mahir-mahota/322-Project-2/SOLIDWORKS_P1/Bearing_H_61952_ma_2.SLDASM

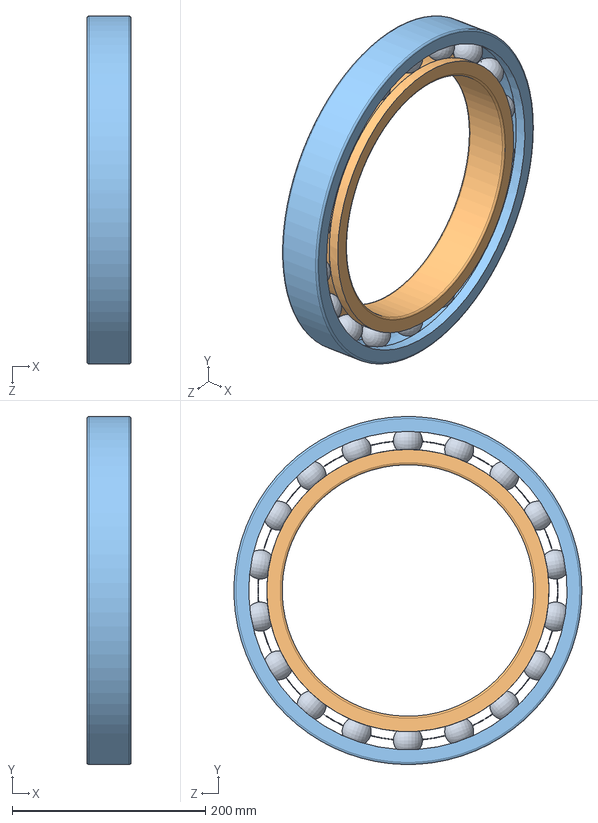
[picture p13: CAD file, 2025-11-18]
SOLIDWORKS_P1/Bearing_H_61952_ma_2.SLDASM
46.0 x 360.0 x 359.8 mm
skf_bearing_61952_ma_2_01
skf_bearing_61952_ma_2_02
skf_bearing_61952_ma_2_03
