mahir-mahota/322-Project-2/SOLIDWORKS_P1/skf_bearing_61952_ma_2_02.SLDPRT

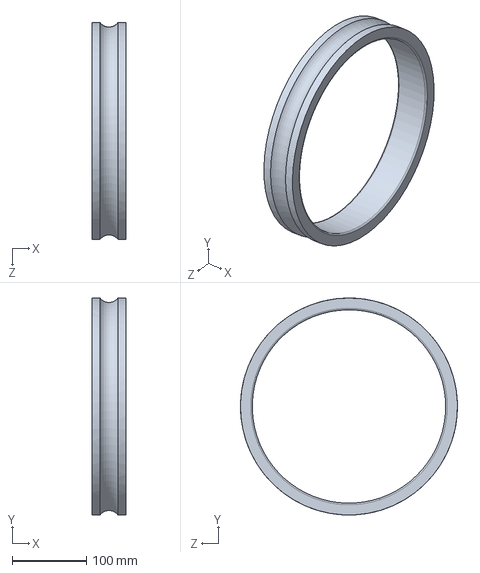
[picture p21: CAD file, 2025-11-18]
SOLIDWORKS_P1/skf_bearing_61952_ma_2_02.SLDPRT
46.0 x 291.9 x 291.8 mm
