mahir-mahota/322-Project-2/SOLIDWORKS_P1/Brg_K_outer_cover2.SLDPRT

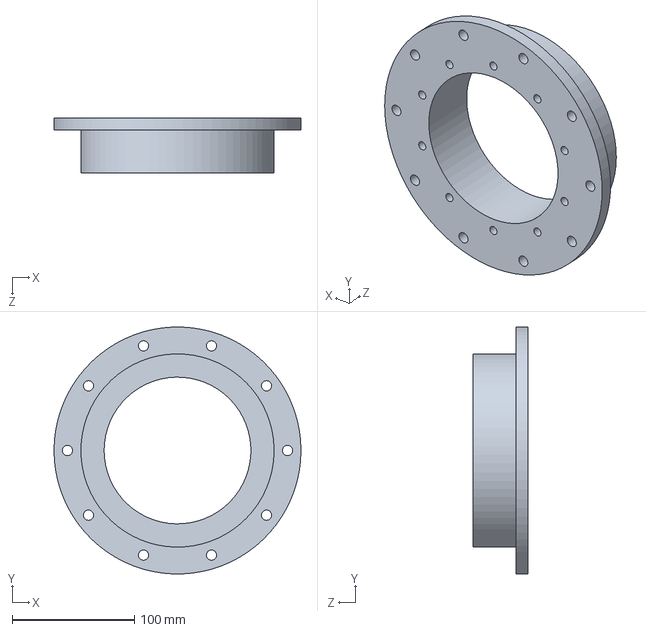
[picture p22: CAD file, 2025-11-18]
SOLIDWORKS_P1/Brg_K_outer_cover2.SLDPRT
202.0 x 201.8 x 45.0 mm
