mahir-mahota/322-Project-2/SOLIDWORKS_P2/Input_shaft_assay_4_Proj2/Input_shaft.SLDPRT

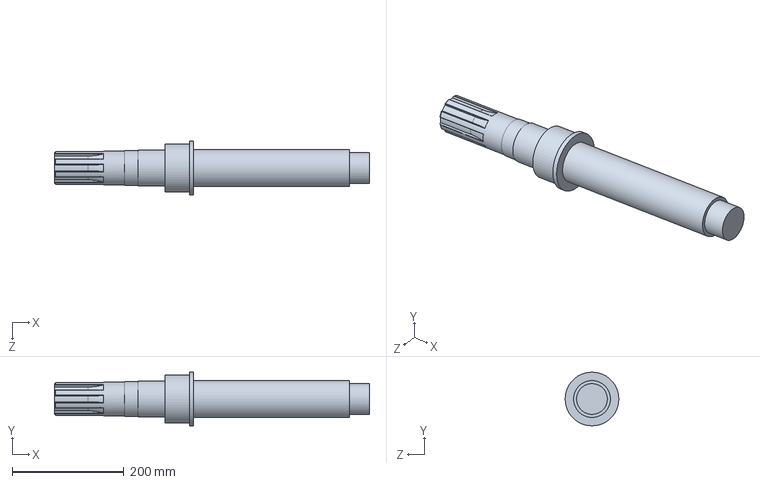
[picture p23: CAD file, 2025-11-28]
SOLIDWORKS_P2/Input_shaft_assay_4_Proj2/Input_shaft.SLDPRT
563.2 x 96.0 x 96.0 mm
