mahir-mahota/322-Project-2/SOLIDWORKS_P1/skf_bearing_na_4840_2_03.SLDPRT

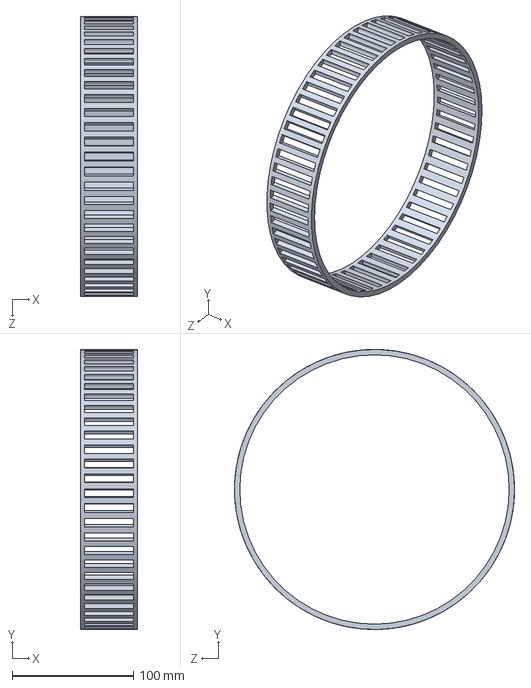
[picture p24: CAD file, 2025-11-18]
SOLIDWORKS_P1/skf_bearing_na_4840_2_03.SLDPRT
47.0 x 230.6 x 230.6 mm
