mahir-mahota/322-Project-2/SOLIDWORKS_P2/Input_shaft_assay_4_Proj2/Housing_input.SLDPRT

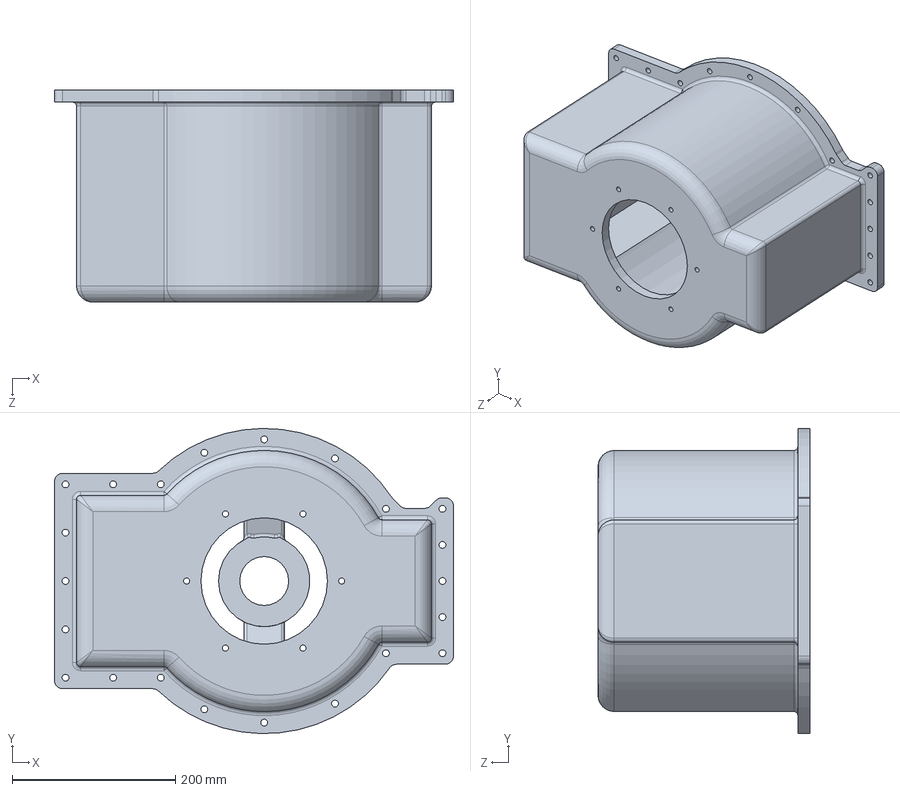
[picture p25: CAD file, 2025-11-28]
SOLIDWORKS_P2/Input_shaft_assay_4_Proj2/Housing_input.SLDPRT
489.0 x 373.9 x 260.0 mm
