mahir-mahota/322-Project-2/SOLIDWORKS_P2/Input_shaft_assay_4_Proj2/Housing_input_cover.SLDPRT

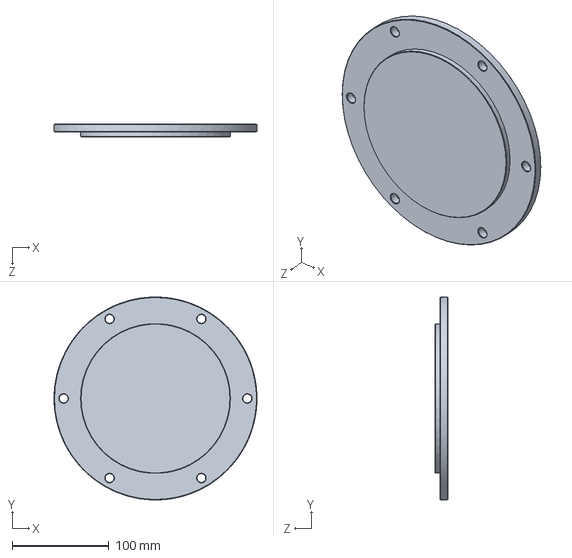
[picture p26: CAD file, 2025-11-20]
SOLIDWORKS_P2/Input_shaft_assay_4_Proj2/Housing_input_cover.SLDPRT
210.0 x 209.9 x 13.0 mm
