mahir-mahota/322-Project-2/SOLIDWORKS_P1/Azi_pinion.SLDPRT

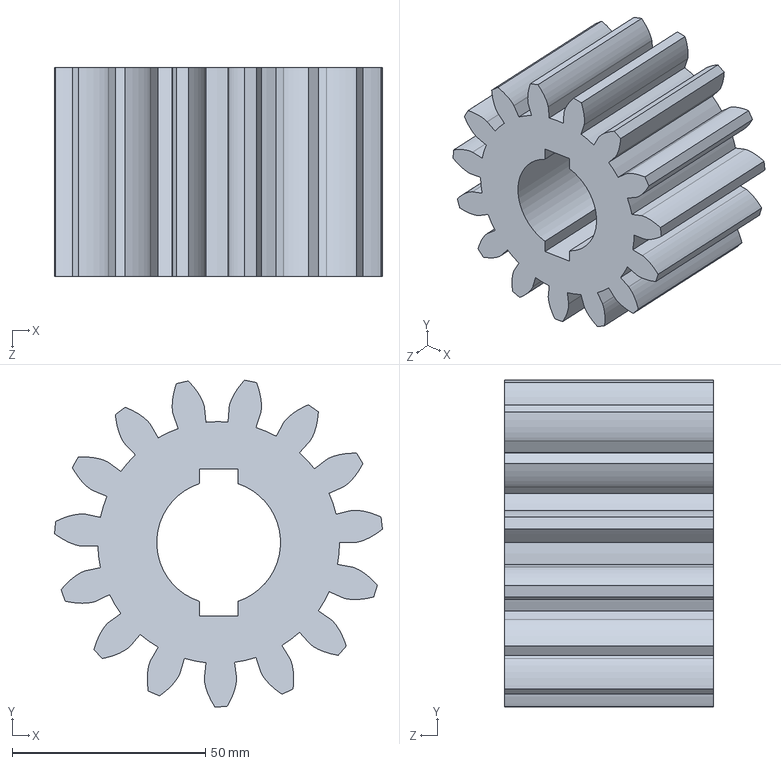
[picture p27: CAD file, 2025-11-18]
SOLIDWORKS_P1/Azi_pinion.SLDPRT
84.8 x 84.5 x 54.0 mm
