mahir-mahota/322-Project-2/SOLIDWORKS_P1/Rudder_tube.SLDPRT

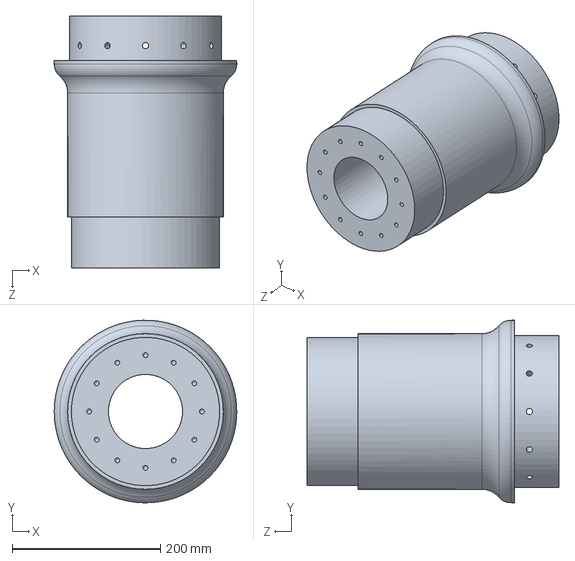
[picture p28: CAD file, 2025-11-18]
SOLIDWORKS_P1/Rudder_tube.SLDPRT
246.3 x 246.3 x 340.0 mm
