mahir-mahota/322-Project-2/SOLIDWORKS_P1/Azi_seal_housing2.SLDPRT

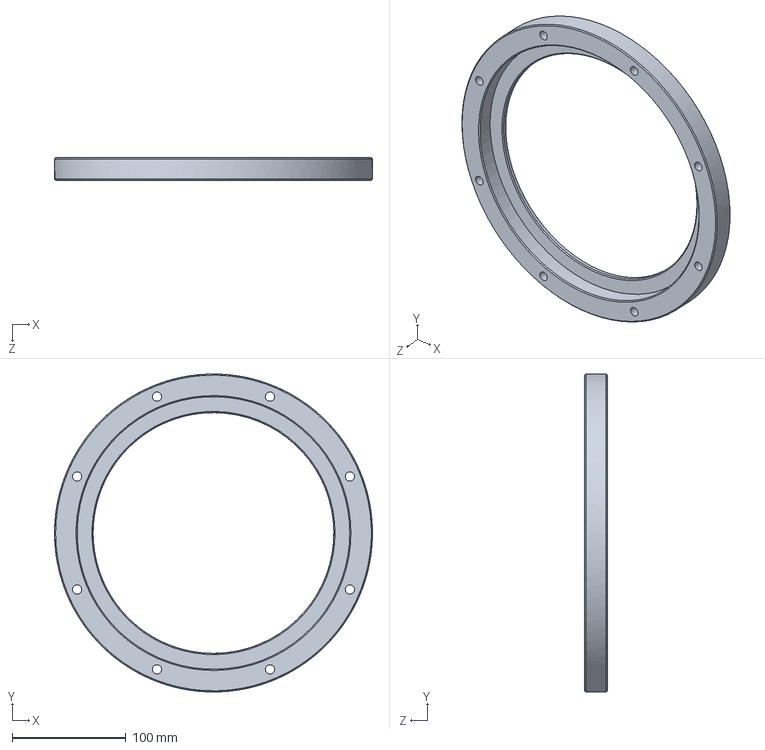
[picture p29: CAD file, 2025-11-18]
SOLIDWORKS_P1/Azi_seal_housing2.SLDPRT
280.0 x 279.9 x 20.0 mm
