mahir-mahota/322-Project-2/SOLIDWORKS_P1/Nozzle.SLDPRT

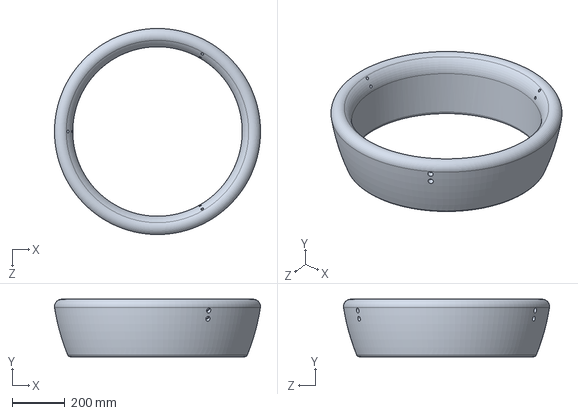
[picture p30: CAD file, 2025-11-18]
SOLIDWORKS_P1/Nozzle.SLDPRT
778.1 x 217.4 x 778.4 mm
