mahir-mahota/322-Project-2/SOLIDWORKS_P1/Coupler.SLDPRT

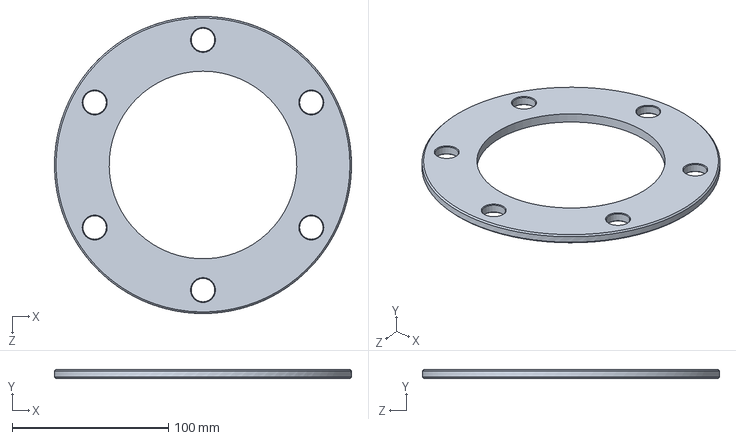
[picture p31: CAD file, 2025-11-18]
SOLIDWORKS_P1/Coupler.SLDPRT
190.0 x 6.00 x 190.0 mm
