mahir-mahota/322-Project-2/SOLIDWORKS_P1/Output_bevel_pinion.SLDPRT

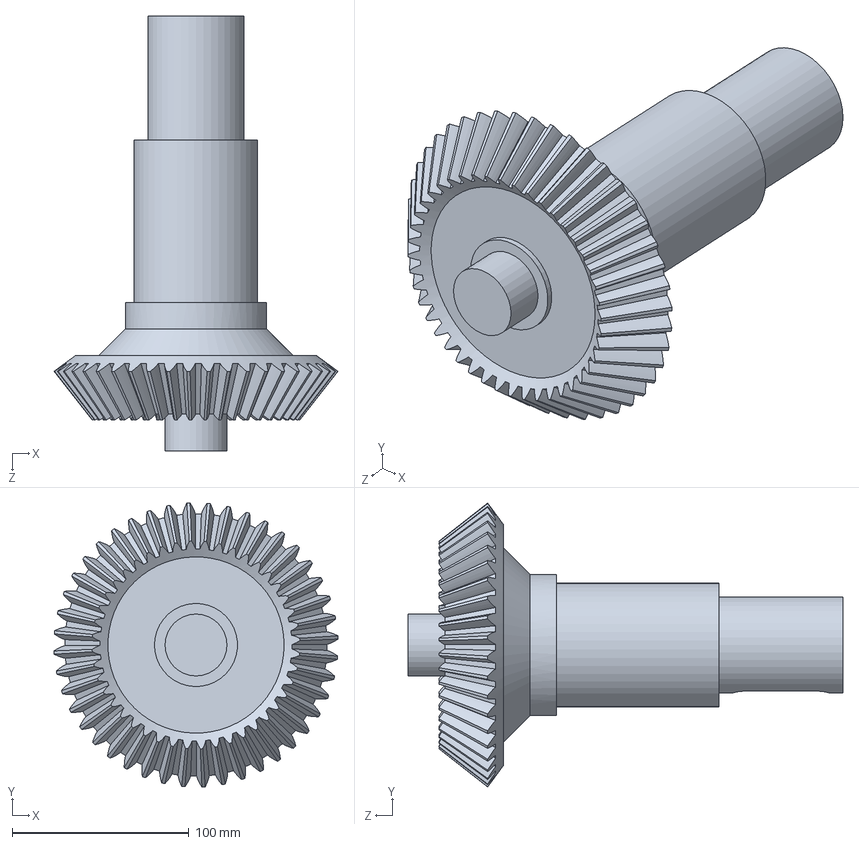
[picture p32: CAD file, 2025-11-18]
SOLIDWORKS_P1/Output_bevel_pinion.SLDPRT
160.7 x 160.7 x 246.0 mm
