mahir-mahota/322-Project-2/SOLIDWORKS_P1/Azi_seal_housing1.SLDPRT

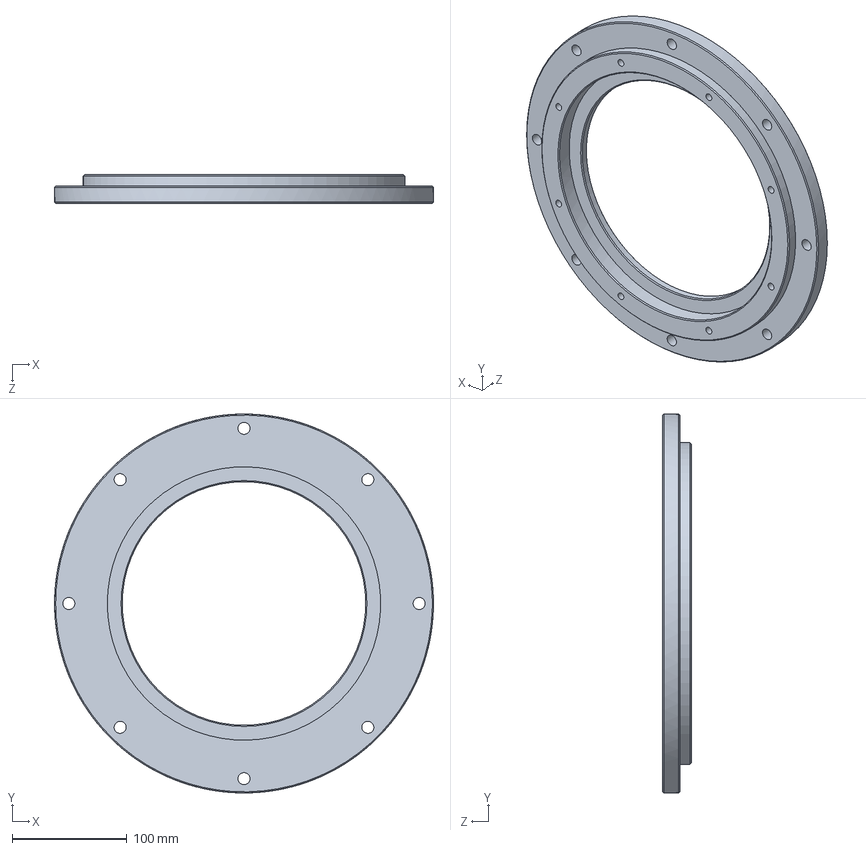
[picture p33: CAD file, 2025-11-18]
SOLIDWORKS_P1/Azi_seal_housing1.SLDPRT
330.0 x 329.9 x 25.0 mm
