mahir-mahota/322-Project-2/SOLIDWORKS_P1/skf_bearing_na_4840_2_01.SLDPRT

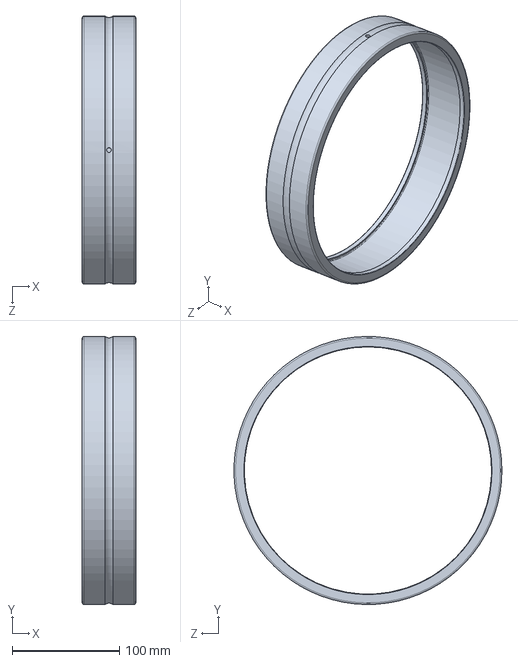
[picture p35: CAD file, 2025-11-18]
SOLIDWORKS_P1/skf_bearing_na_4840_2_01.SLDPRT
50.0 x 250.0 x 249.9 mm
