mahir-mahota/322-Project-2/SOLIDWORKS_P1/skf_bearing_61952_ma_2_03.SLDPRT

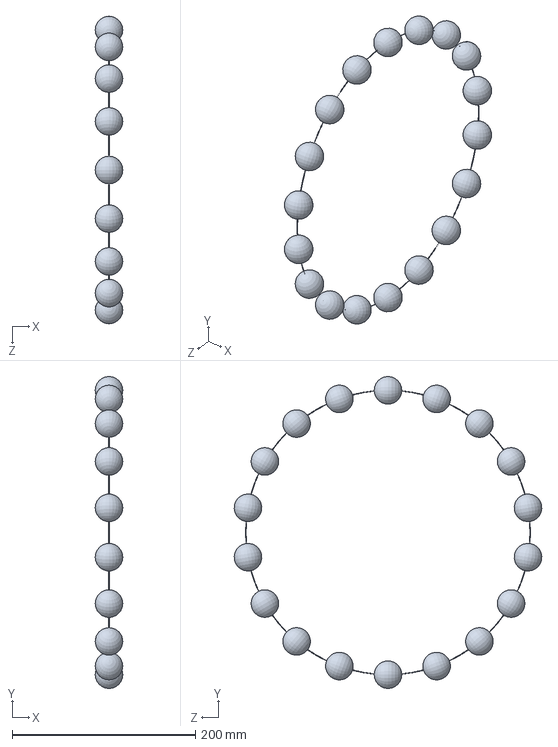
[picture p36: CAD file, 2025-11-18]
SOLIDWORKS_P1/skf_bearing_61952_ma_2_03.SLDPRT
30.2 x 340.2 x 335.3 mm
