mahir-mahota/322-Project-2/SOLIDWORKS_P1/Blade.SLDPRT

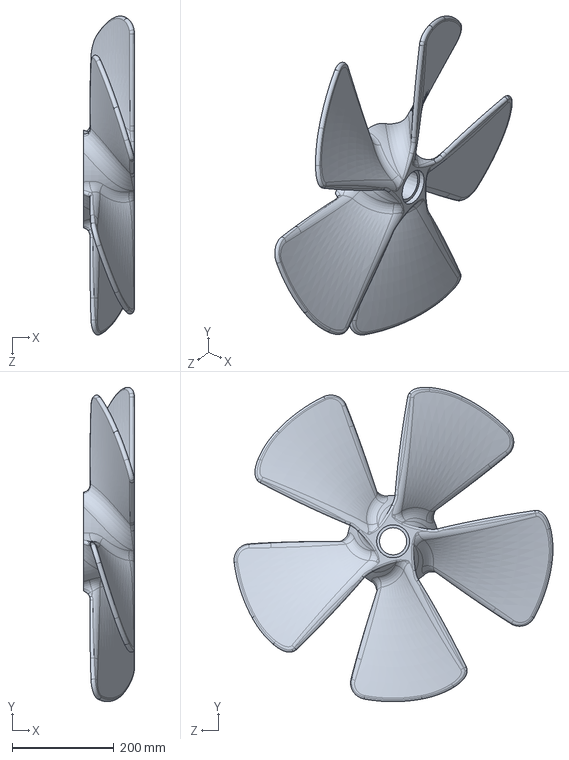
[picture p37: CAD file, 2025-11-18]
SOLIDWORKS_P1/Blade.SLDPRT
100.0 x 617.5 x 626.6 mm
