mahir-mahota/322-Project-2/SOLIDWORKS_P1/skf_bearing_na_4840_2_04.SLDPRT

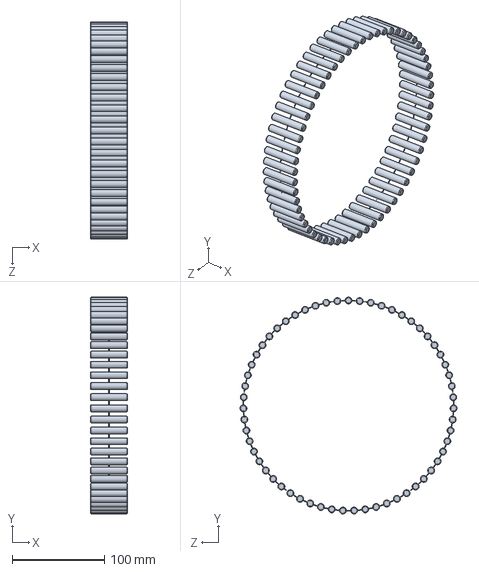
[picture p38: CAD file, 2025-11-18]
SOLIDWORKS_P1/skf_bearing_na_4840_2_04.SLDPRT
40.0 x 234.8 x 234.9 mm
