mahir-mahota/322-Project-2/SOLIDWORKS_P1/SKF_Locknut_KM13.SLDPRT

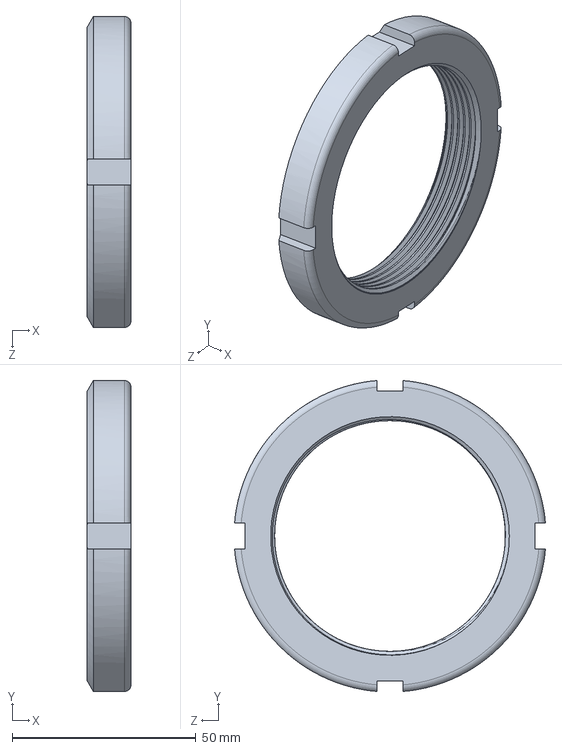
[picture p39: CAD file, 2025-11-18]
SOLIDWORKS_P1/SKF_Locknut_KM13.SLDPRT
12.0 x 84.7 x 84.7 mm
