mahir-mahota/322-Project-2/SOLIDWORKS_P1/Brg_K_outer_cover1.SLDPRT

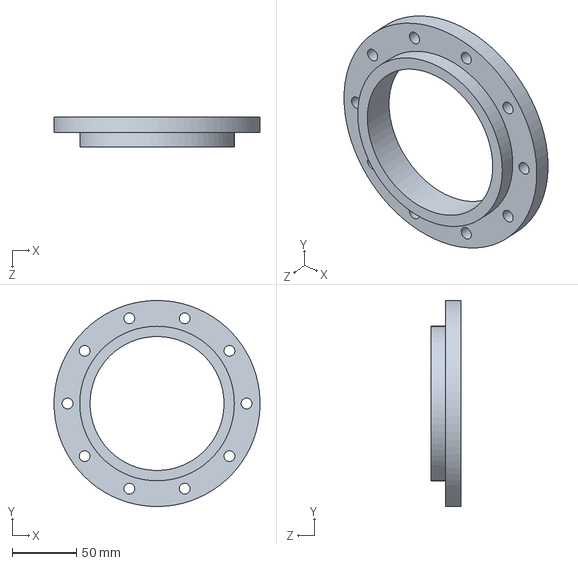
[picture p40: CAD file, 2025-11-18]
SOLIDWORKS_P1/Brg_K_outer_cover1.SLDPRT
159.9 x 160.0 x 23.0 mm
