mahir-mahota/322-Project-2/SOLIDWORKS_P1/Counter_shaft.SLDPRT

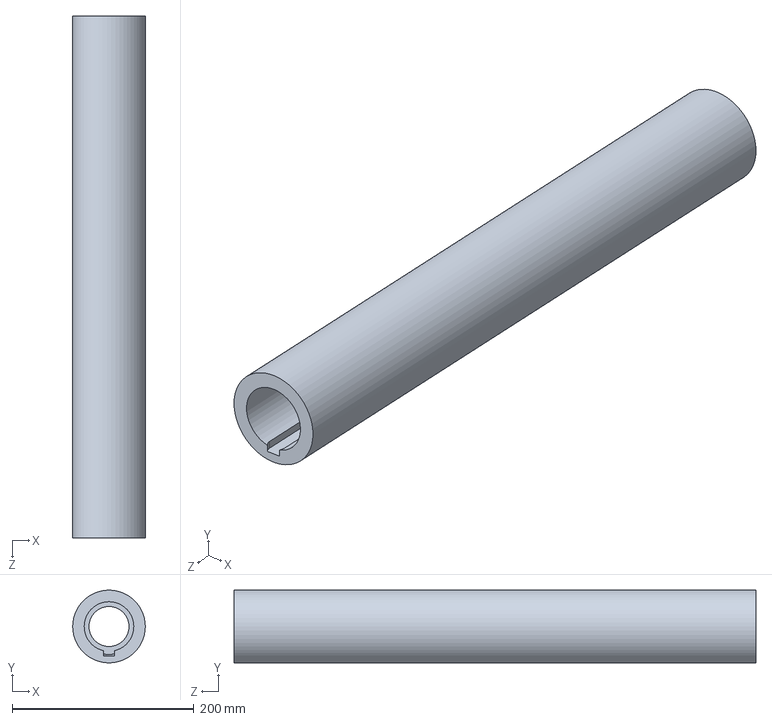
[picture p41: CAD file, 2025-11-18]
SOLIDWORKS_P1/Counter_shaft.SLDPRT
80.0 x 79.9 x 574.5 mm
