mahir-mahota/322-Project-2/SOLIDWORKS_P1/Input_shaft.SLDPRT

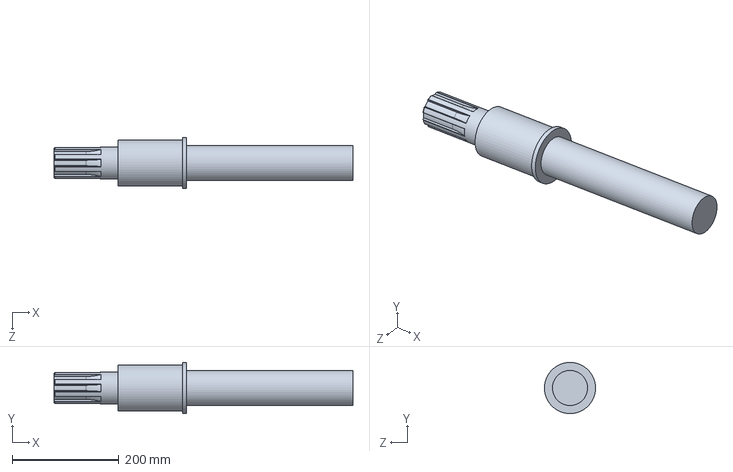
[picture p42: CAD file, 2025-11-18]
SOLIDWORKS_P1/Input_shaft.SLDPRT
561.4 x 96.0 x 96.0 mm
