mahir-mahota/322-Project-2/SOLIDWORKS_P1/azimuth_motor_shaft.SLDPRT

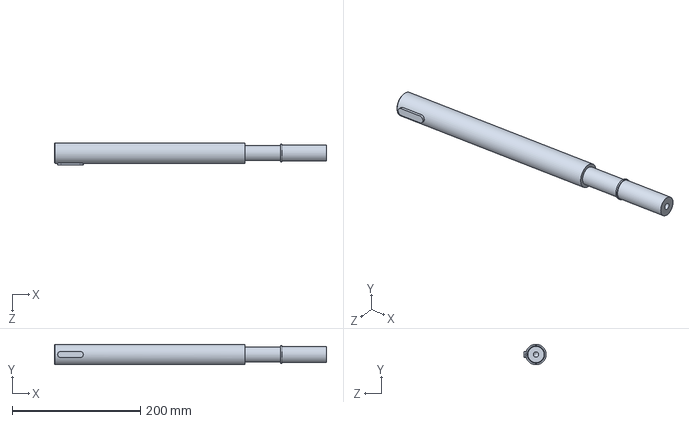
[picture p43: CAD file, 2025-11-18]
SOLIDWORKS_P1/azimuth_motor_shaft.SLDPRT
425.0 x 32.0 x 35.0 mm
