mahir-mahota/322-Project-2/SOLIDWORKS_P1/Output_shaft.SLDPRT

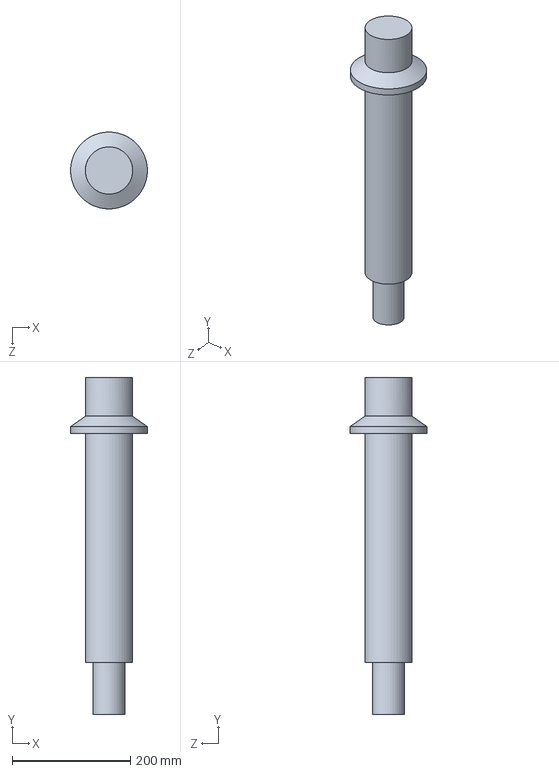
[picture p44: CAD file, 2025-11-18]
SOLIDWORKS_P1/Output_shaft.SLDPRT
130.0 x 570.0 x 130.0 mm
