mahir-mahota/322-Project-2/SOLIDWORKS_P1/Spline_4_input_shaft.SLDPRT

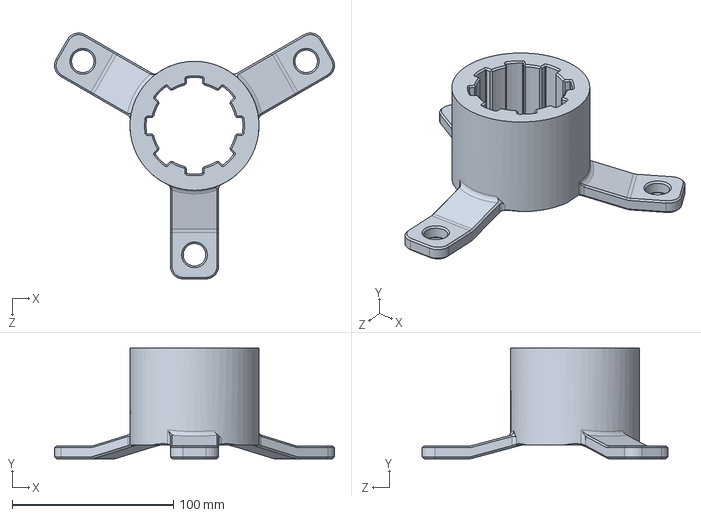
[picture p45: CAD file, 2025-11-18]
SOLIDWORKS_P1/Spline_4_input_shaft.SLDPRT
173.6 x 68.7 x 152.5 mm
