mahir-mahota/322-Project-2/SOLIDWORKS_P1/skf_bearing_na_4840_2_02.SLDPRT

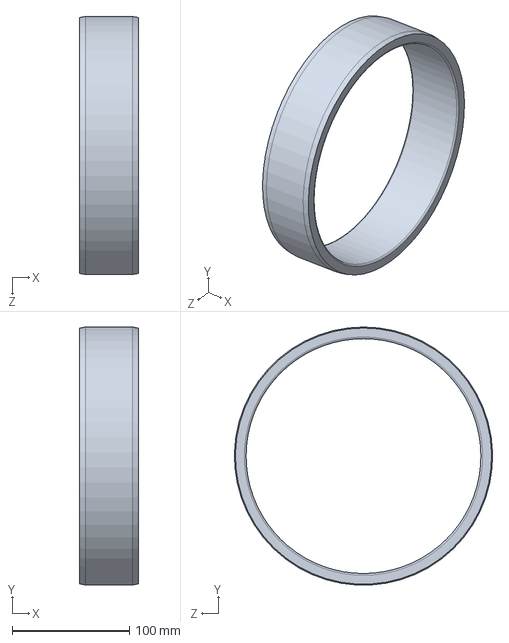
[picture p46: CAD file, 2025-11-18]
SOLIDWORKS_P1/skf_bearing_na_4840_2_02.SLDPRT
50.0 x 219.8 x 219.9 mm
