mahir-mahota/322-Project-2/SOLIDWORKS_P1/SKF_210X240X15 HMS5 RG Spring.SLDPRT

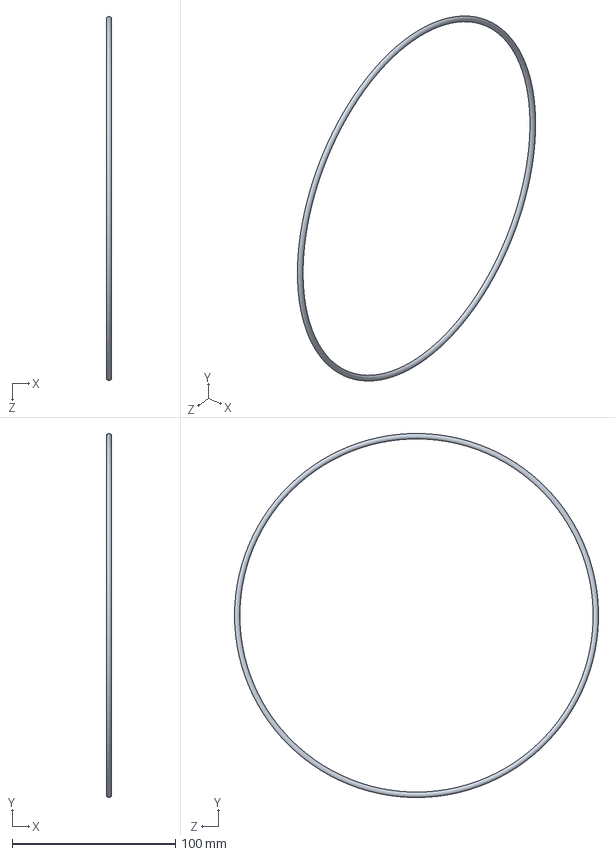
[picture p47: CAD file, 2025-11-18]
SOLIDWORKS_P1/SKF_210X240X15 HMS5 RG Spring.SLDPRT
3.33 x 223.3 x 223.3 mm
