mahir-mahota/322-Project-2/SOLIDWORKS_P1/skf_bearing_61952_ma_2_01.SLDPRT

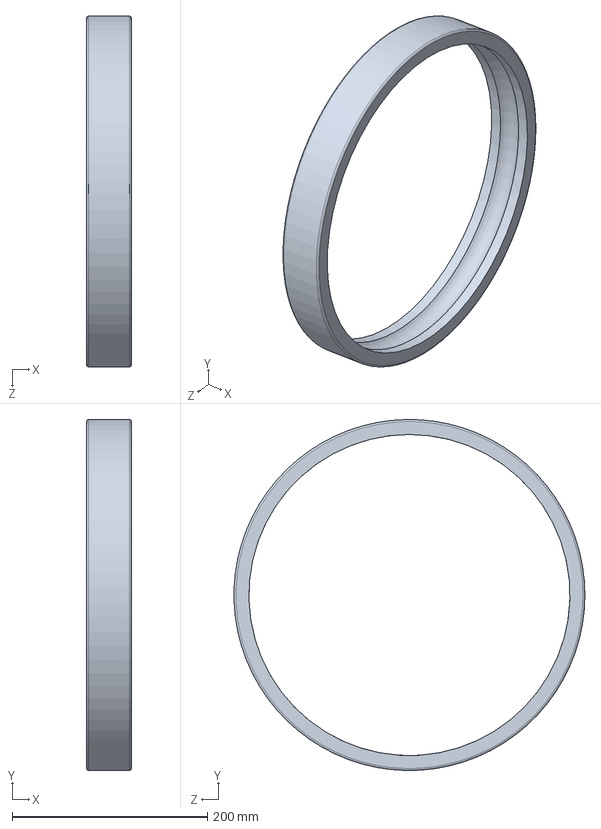
[picture p48: CAD file, 2025-11-18]
SOLIDWORKS_P1/skf_bearing_61952_ma_2_01.SLDPRT
46.0 x 360.0 x 359.8 mm
