mahir-mahota/322-Project-2/SOLIDWORKS_P1/Blade_clamp.SLDPRT

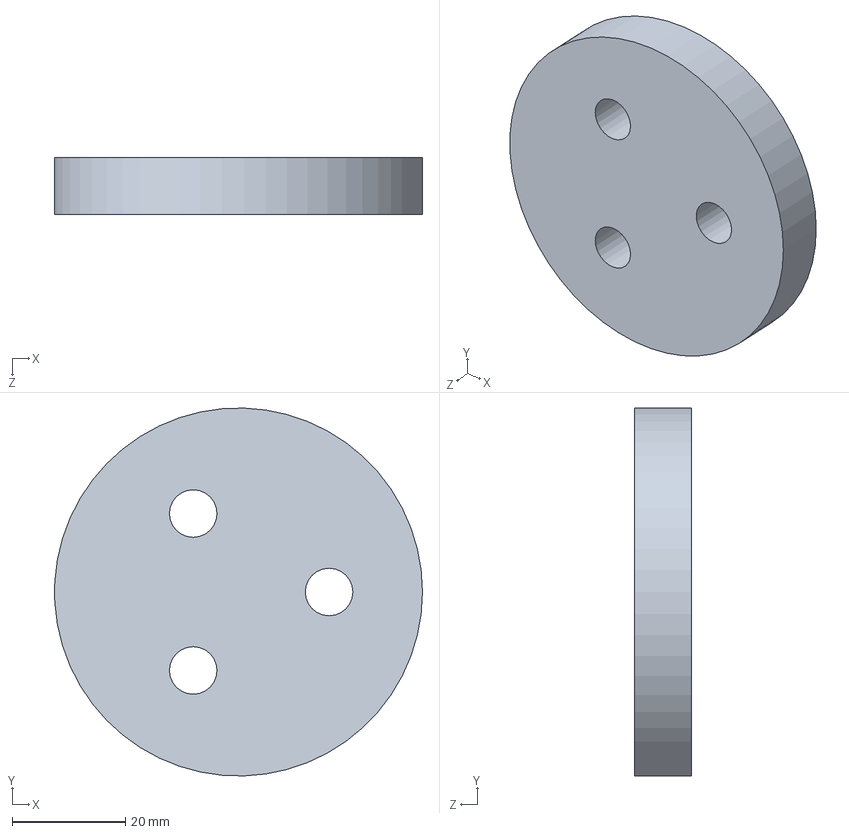
[picture p49: CAD file, 2025-11-18]
SOLIDWORKS_P1/Blade_clamp.SLDPRT
65.0 x 65.0 x 10.0 mm
