mahir-mahota/322-Project-2/SOLIDWORKS_P1/Brg_H_inner_cover.SLDPRT

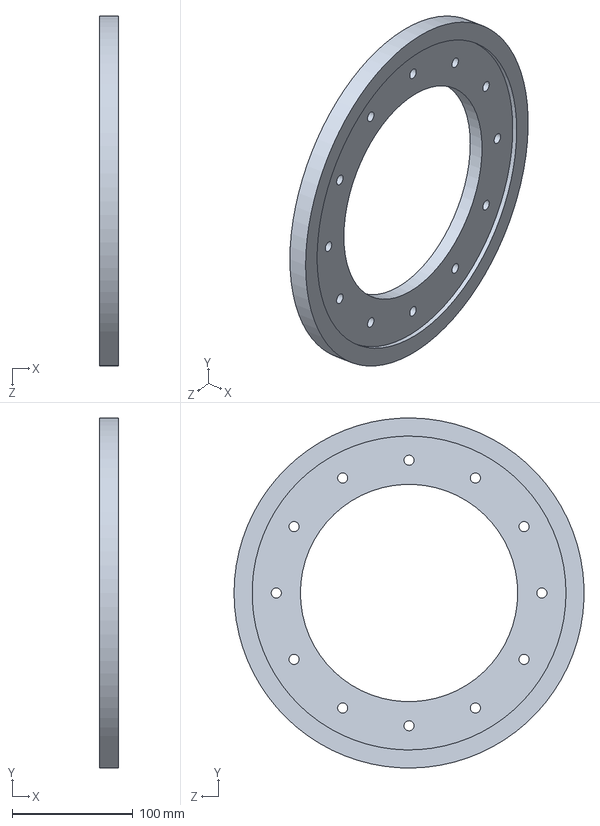
[picture p50: CAD file, 2025-11-18]
SOLIDWORKS_P1/Brg_H_inner_cover.SLDPRT
16.0 x 289.9 x 289.9 mm
