mahir-mahota/322-Project-2/SOLIDWORKS_P1/mill qill  handle.SLDPRT

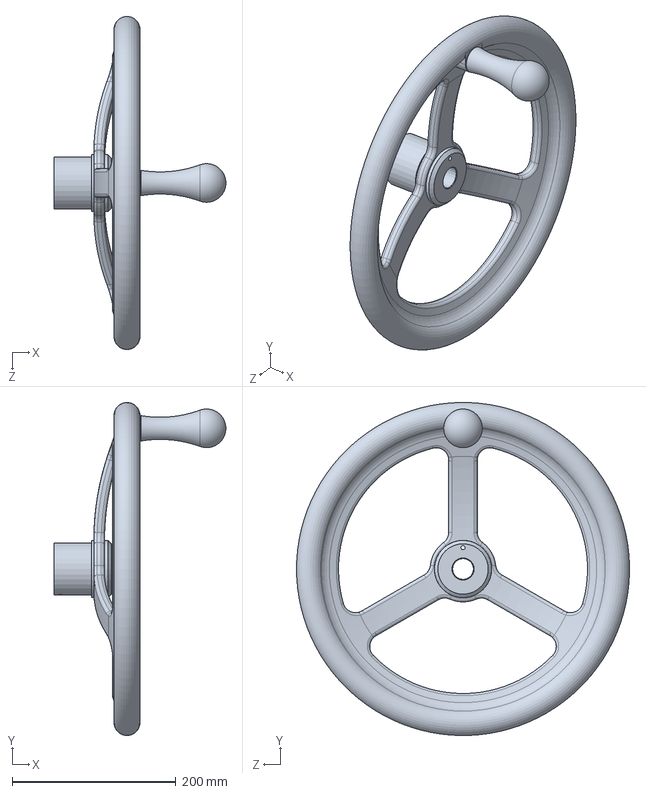
[picture p51: CAD file, 2025-11-18]
SOLIDWORKS_P1/mill qill handle.SLDPRT
209.5 x 406.2 x 406.2 mm
