mahir-mahota/322-Project-2/SOLIDWORKS_P1/Spline_thr_motor.SLDPRT

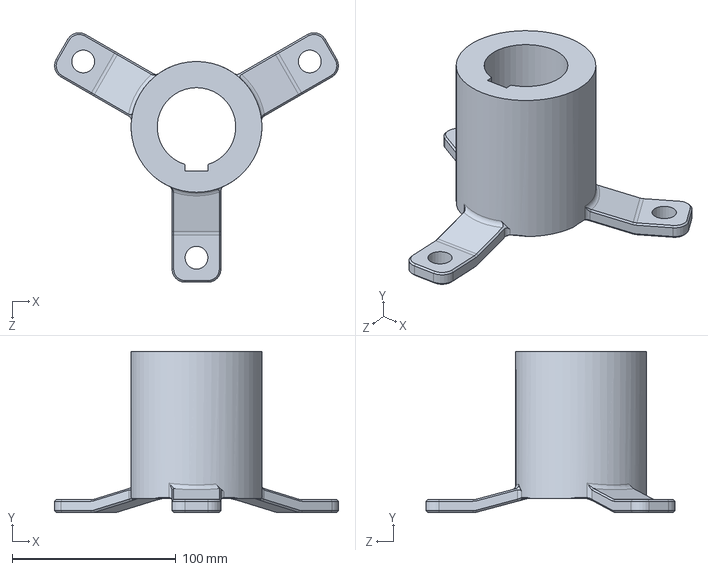
[picture p52: CAD file, 2025-11-18]
SOLIDWORKS_P1/Spline_thr_motor.SLDPRT
173.7 x 98.7 x 152.6 mm
