mahir-mahota/322-Project-2/SOLIDWORKS_P1/thrust_motor_shaft.SLDPRT

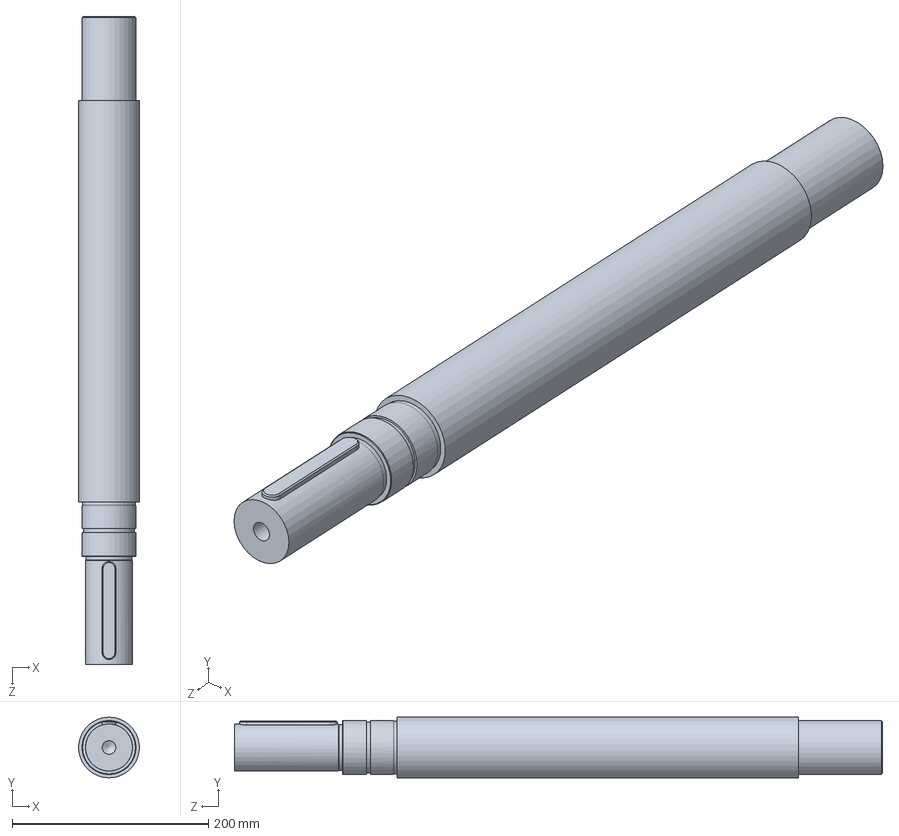
[picture p53: CAD file, 2025-11-18]
SOLIDWORKS_P1/thrust_motor_shaft.SLDPRT
61.7 x 62.0 x 661.0 mm
