mahir-mahota/322-Project-2/SOLIDWORKS_P1/Output_bevel_gear.SLDPRT

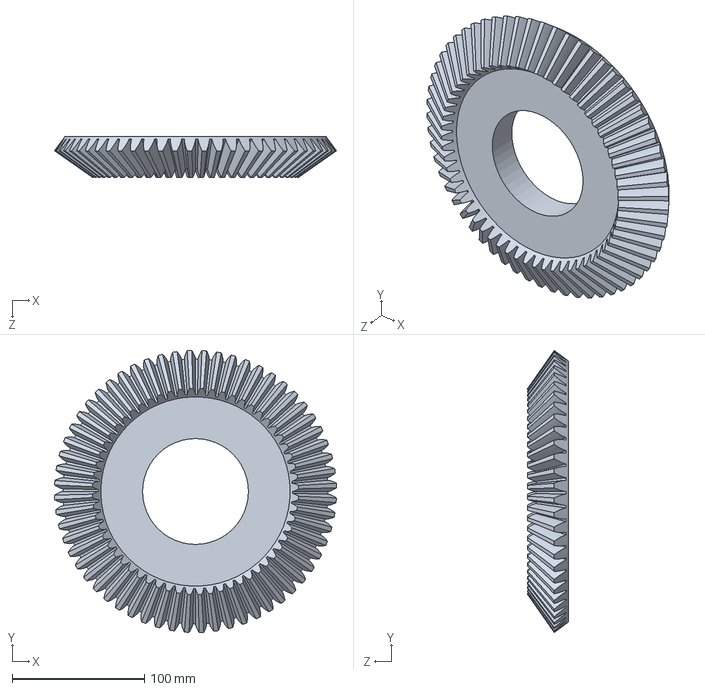
[picture p54: CAD file, 2025-11-18]
SOLIDWORKS_P1/Output_bevel_gear.SLDPRT
213.2 x 213.2 x 30.8 mm
