mahir-mahota/322-Project-2/SOLIDWORKS_P1/Nozzle_rim.SLDPRT

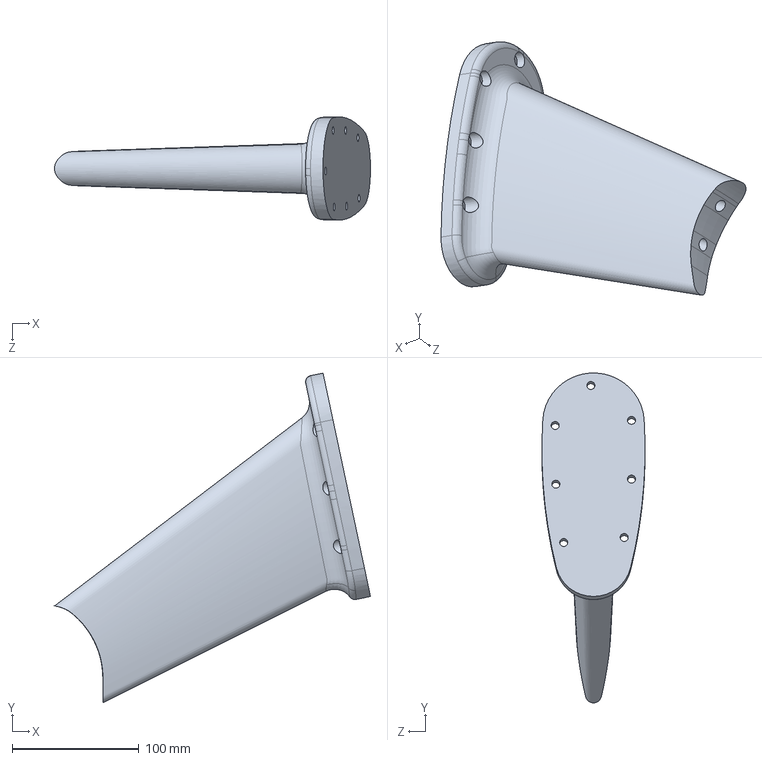
[picture p55: CAD file, 2025-11-18]
SOLIDWORKS_P1/Nozzle_rim.SLDPRT
249.0 x 259.8 x 81.3 mm
