mahir-mahota/322-Project-2/SOLIDWORKS_P1/Lower_dome.SLDPRT

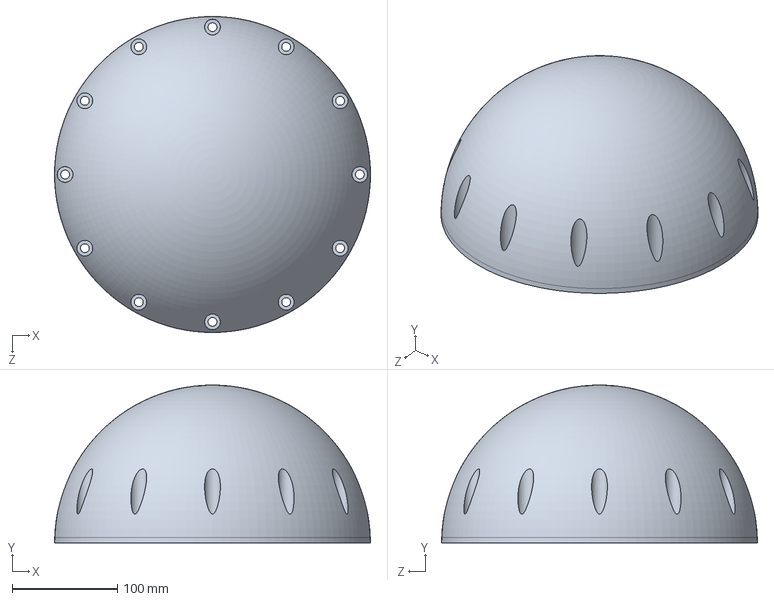
[picture p56: CAD file, 2025-11-18]
SOLIDWORKS_P1/Lower_dome.SLDPRT
300.2 x 150.0 x 300.2 mm
