mahir-mahota/322-Project-2/SOLIDWORKS_P1/Azi_gear.SLDPRT

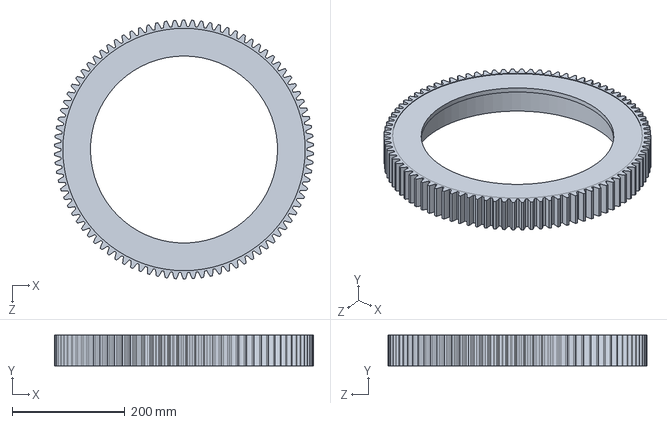
[picture p57: CAD file, 2025-11-18]
SOLIDWORKS_P1/Azi_gear.SLDPRT
459.9 x 55.0 x 460.0 mm
