mahir-mahota/322-Project-2/SOLIDWORKS_P1/Bearing_GK_NSK_HR33114J.SLDASM

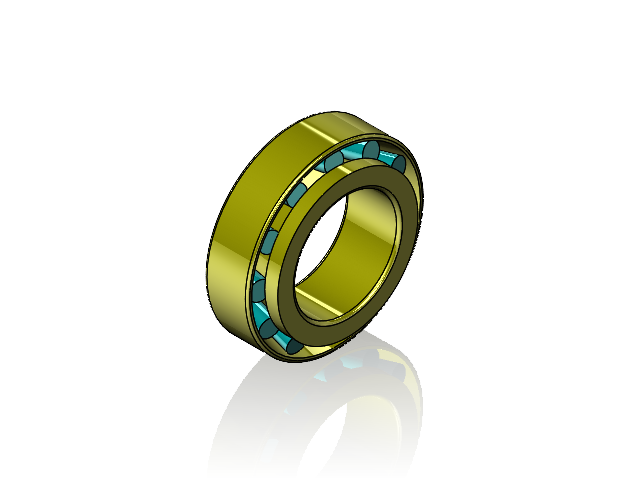
[picture p64: CAD file, 2025-11-18]
SOLIDWORKS_P1/Bearing_GK_NSK_HR33114J.SLDASM
HR33114J Inner ring
HR33114J Outer ring
