mahir-mahota/322-Project-2/SOLIDWORKS_P1/Assem Quill Handle.SLDASM

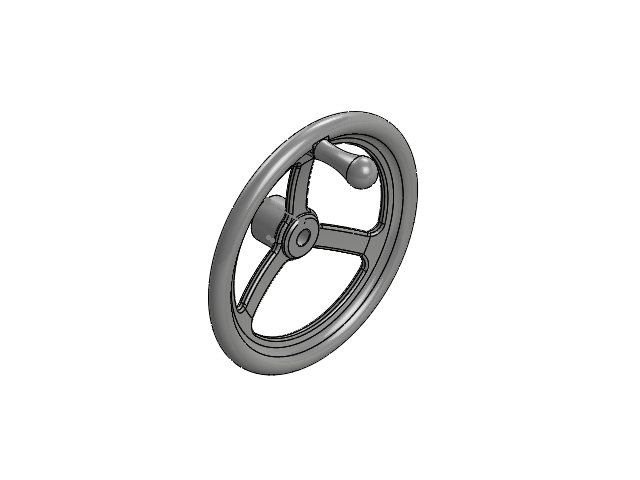
[picture p65: CAD file, 2025-11-18]
SOLIDWORKS_P1/Assem Quill Handle.SLDASM
mill qill handle
91595A399_METRIC ALLOY STEEL DOWEL PIN
3408A220_BALL-NOSE SPRING PLUNGER W SS BALL
