mahir-mahota/322-Project-2/SOLIDWORKS_P1/azimuth_motor.SLDASM

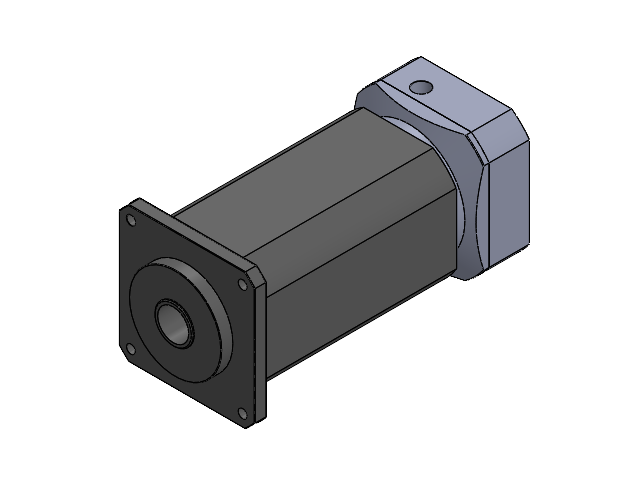
[picture p66: CAD file, 2025-11-18]
SOLIDWORKS_P1/azimuth_motor.SLDASM
96200010_connect
96200010_back
96200010_front_wo_shaft
